sasukeop108/ClockX-V1/Photos/leftview.png

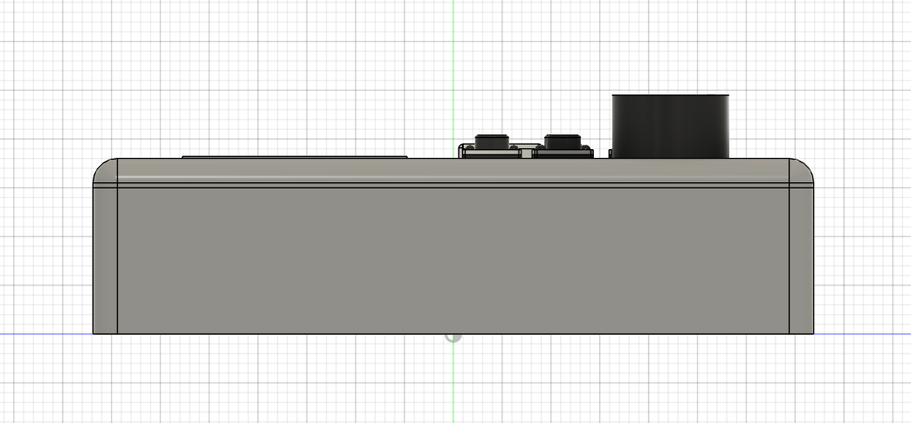
Photos/leftview.png
