sasukeop108/ClockX-V1/BOM/makerbazaar2.png

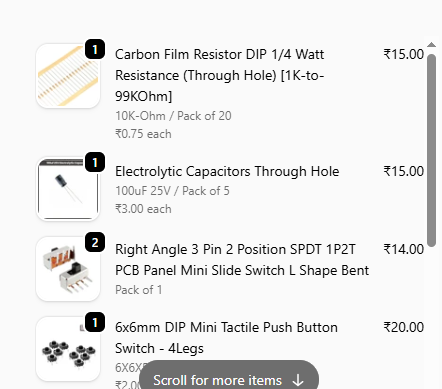
BOM/makerbazaar2.png
