sasukeop108/ClockX-V1/BOM/makerbazaar3.png

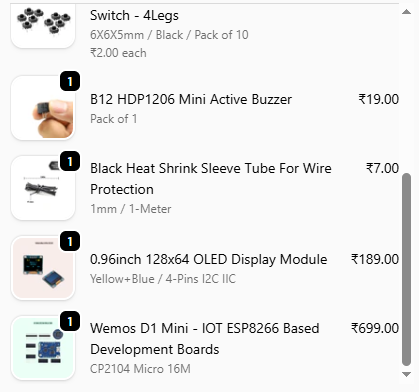
BOM/makerbazaar3.png
