sasukeop108/ClockX-V1/BOM/makerbazaar4.png

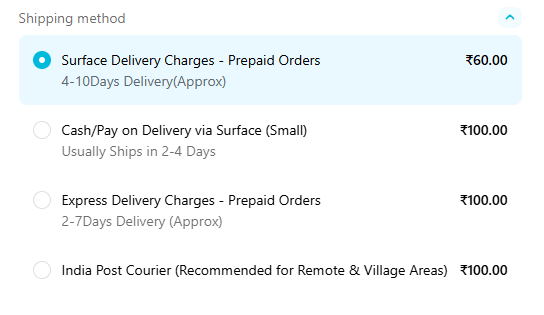
BOM/makerbazaar4.png
