sasukeop108/ClockX-V1/BOM/Makerbazaar.png

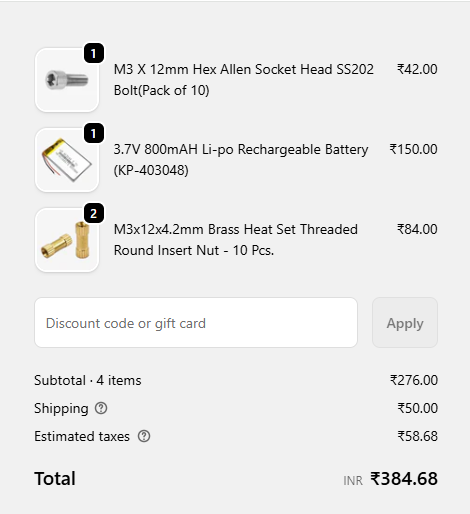
BOM/Makerbazaar.png
